NaysanMunje/Hexapod-Robot/pca_servo_test/gen_walk_html.py

# Rebuild include/gait_preview_html.h from www/walk.html
# Run after editing the gait preview page:
#   python gen_walk_html.py
from pathlib import Path

ROOT = Path(__file__).resolve().parent
html_path = ROOT / "www" / "walk.html"
out_path = ROOT / "include" / "gait_preview_html.h"
html = html_path.read_text(encoding="utf-8")
if ")HTML" in html:
    raise SystemExit("walk.html contains )HTML — pick another delimiter")
out_path.write_text(
    "#pragma once\n"
    "#include <Arduino.h>\n\n"
    'static const char WALK_HTML[] PROGMEM = R"HTML(\n'
    + html
    + '\n)HTML";\n',
    encoding="utf-8",
)
print(f"wrote {out_path} ({out_path.stat().st_size} bytes)")
